The-Open-Music-Box/raspberrypi-firmware/back/app/src/domain/protocols/event_bus_protocol.py

# Copyright (c) 2025 Jonathan Piette
# This file is part of TheOpenMusicBox and is licensed for non-commercial use only.
# See the LICENSE file for details.

"""Event bus protocol for domain events."""

from abc import abstractmethod
from collections.abc import Callable
from dataclasses import dataclass
from datetime import datetime
from typing import Any, Protocol


@dataclass
class AudioEvent:
    """Base class for all audio domain events."""

    def __init__(self, source_component: str):
        self.source_component = source_component
        self.timestamp = datetime.now()


class EventBusProtocol(Protocol):
    """Protocol for event bus operations.

    Handles domain events and notifications.
    """

    @abstractmethod
    async def publish(self, event: AudioEvent) -> None:
        """Publish an event.

        Args:
            event: The event to publish
        """
        ...

    @abstractmethod
    def subscribe(self, event_type: type[AudioEvent], handler: Callable[[AudioEvent], Any]) -> None:
        """Subscribe to an event type.

        Args:
            event_type: Type of event to subscribe to
            handler: Event handler function
        """
        ...

    @abstractmethod
    def unsubscribe(self, event_type: type[AudioEvent], handler: Callable[[AudioEvent], Any]) -> None:
        """Unsubscribe from an event type.

        Args:
            event_type: Type of event to unsubscribe from
            handler: Event handler function to remove
        """
        ...
