The-Open-Music-Box/raspberrypi-firmware/back/tests/contracts/openapi.yaml

openapi: 3.0.3
info:
  title: TheOpenMusicBox API
  description: |
    Complete API contract definitions for TheOpenMusicBox - A Raspberry Pi-based music player system.

    All API responses follow the UnifiedResponseService format with standardized envelopes.
    This specification is the source of truth for all client implementations (Web, Flutter, C++).
  version: 4.1.0
  contact:
    name: TheOpenMusicBox
    url: https://github.com/theopenmusicbox/tomb-rpi
  license:
    name: MIT

servers:
  - url: http://localhost:8000
    description: Local development server
  - url: http://{host}:8000
    description: Custom deployment
    variables:
      host:
        default: localhost
        description: Raspberry Pi hostname or IP address

tags:
  - name: Health
    description: Health check endpoints
  - name: Player
    description: Audio player control endpoints
  - name: Playlists
    description: Playlist management endpoints
  - name: NFC
    description: NFC tag association endpoints
  - name: System
    description: System information and control
  - name: YouTube
    description: YouTube download functionality
  - name: Uploads
    description: File upload management

components:
  schemas:
    UnifiedResponse:
      type: object
      description: Standardized response wrapper used by all API endpoints
      required:
        - status
        - message
        - timestamp
      properties:
        status:
          type: string
          enum: [success, error]
        message:
          type: string
        data:
          oneOf:
            - type: object
            - type: array
              items: {}
            - type: "null"
        client_op_id:
          type: string
          nullable: true
          description: Client operation ID for operation tracking
        server_seq:
          type: number
          nullable: true
          description: Server sequence number for state synchronization
        timestamp:
          type: number
          description: Unix timestamp in seconds
        request_id:
          type: string
          nullable: true
        error_type:
          type: string
          nullable: true
          enum:
            - validation_error
            - not_found
            - rate_limit_exceeded
            - service_unavailable
            - internal_error
            - conflict
            - bad_request
        details:
          type: object
          nullable: true
          additionalProperties: true

    Track:
      type: object
      required:
        - track_number
        - title
        - filename
      properties:
        track_number:
          type: integer
          description: Track number in playlist (1-based position)
        title:
          type: string
        filename:
          type: string
        file_path:
          type: string
        duration:
          type: integer
          nullable: true
          deprecated: true
          description: |
            DEPRECATED: Use duration_ms instead for millisecond precision.
            Duration in seconds. Will be removed in a future version.
        duration_ms:
          type: integer
          nullable: true
          description: Duration in milliseconds (preferred over duration)
        artist:
          type: string
          nullable: true
        album:
          type: string
          nullable: true
        file_size:
          type: integer
          nullable: true
        created_at:
          type: string
          format: date-time
        updated_at:
          type: string
          format: date-time

    PlaylistSummary:
      type: object
      required:
        - id
        - title
        - track_count
      properties:
        id:
          type: string
        title:
          type: string
        track_count:
          type: integer
        nfc_tag_id:
          type: string
          nullable: true
        server_seq:
          type: number
        created_at:
          type: string
          format: date-time
        updated_at:
          type: string
          format: date-time

    PlaylistDetailed:
      type: object
      required:
        - id
        - title
        - tracks
      properties:
        id:
          type: string
        title:
          type: string
        description:
          type: string
        tracks:
          type: array
          items:
            $ref: '#/components/schemas/Track'
        nfc_tag_id:
          type: string
          nullable: true
        server_seq:
          type: number
        created_at:
          type: string
          format: date-time
        updated_at:
          type: string
          format: date-time
        total_duration_ms:
          type: integer
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
